khinds10/SolarBar/gradients/1.png

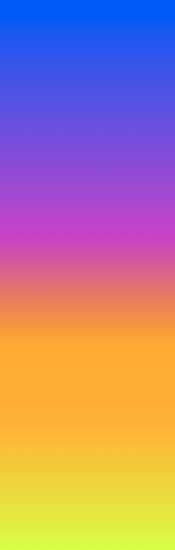
gradients/1.png
