khinds10/SolarBar/gradients/2.png

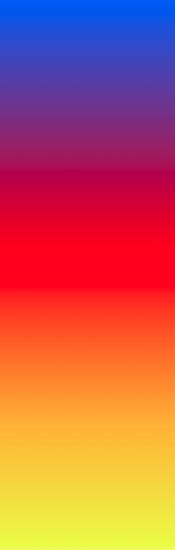
gradients/2.png
