khinds10/SolarBar/gradients/3.png

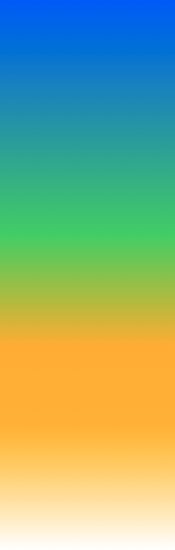
gradients/3.png
