khinds10/SolarBar/gradients/5.png

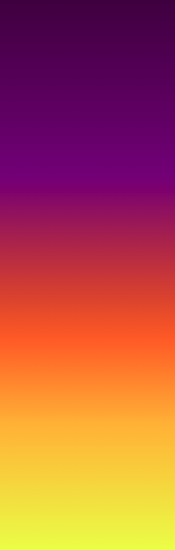
gradients/5.png
